1ee7/OpenCloudEnvMonitor/Doc/hardware/Nordic开发板资料/nRF51822AKII/原理图/USBDongle原理图_PCB.PDF

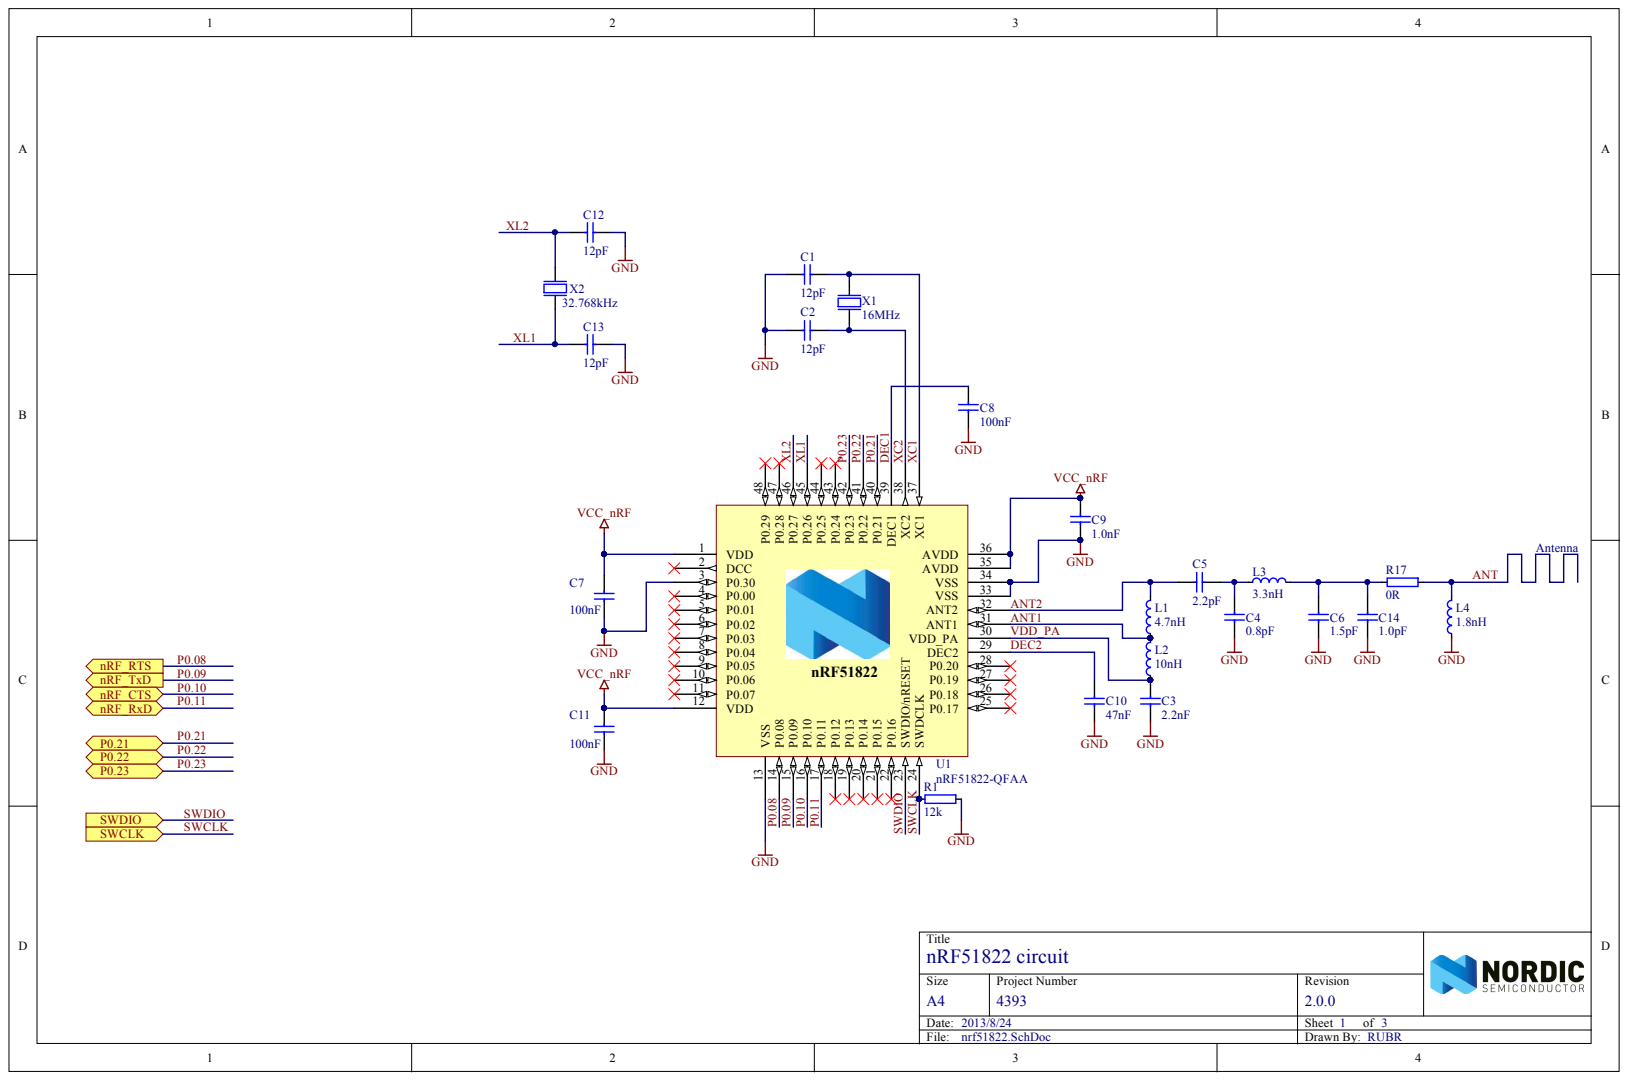
[picture p52: page 1]

VDD_P A
DEC 2

Title Size nRF51822 circuit

A4 | P roje ct Numbe r 4393 | R evision 2.0.0

Date : 2013/8/24 | She et of
File : nr f51822. S chDoc | Dr awn By: RUB R

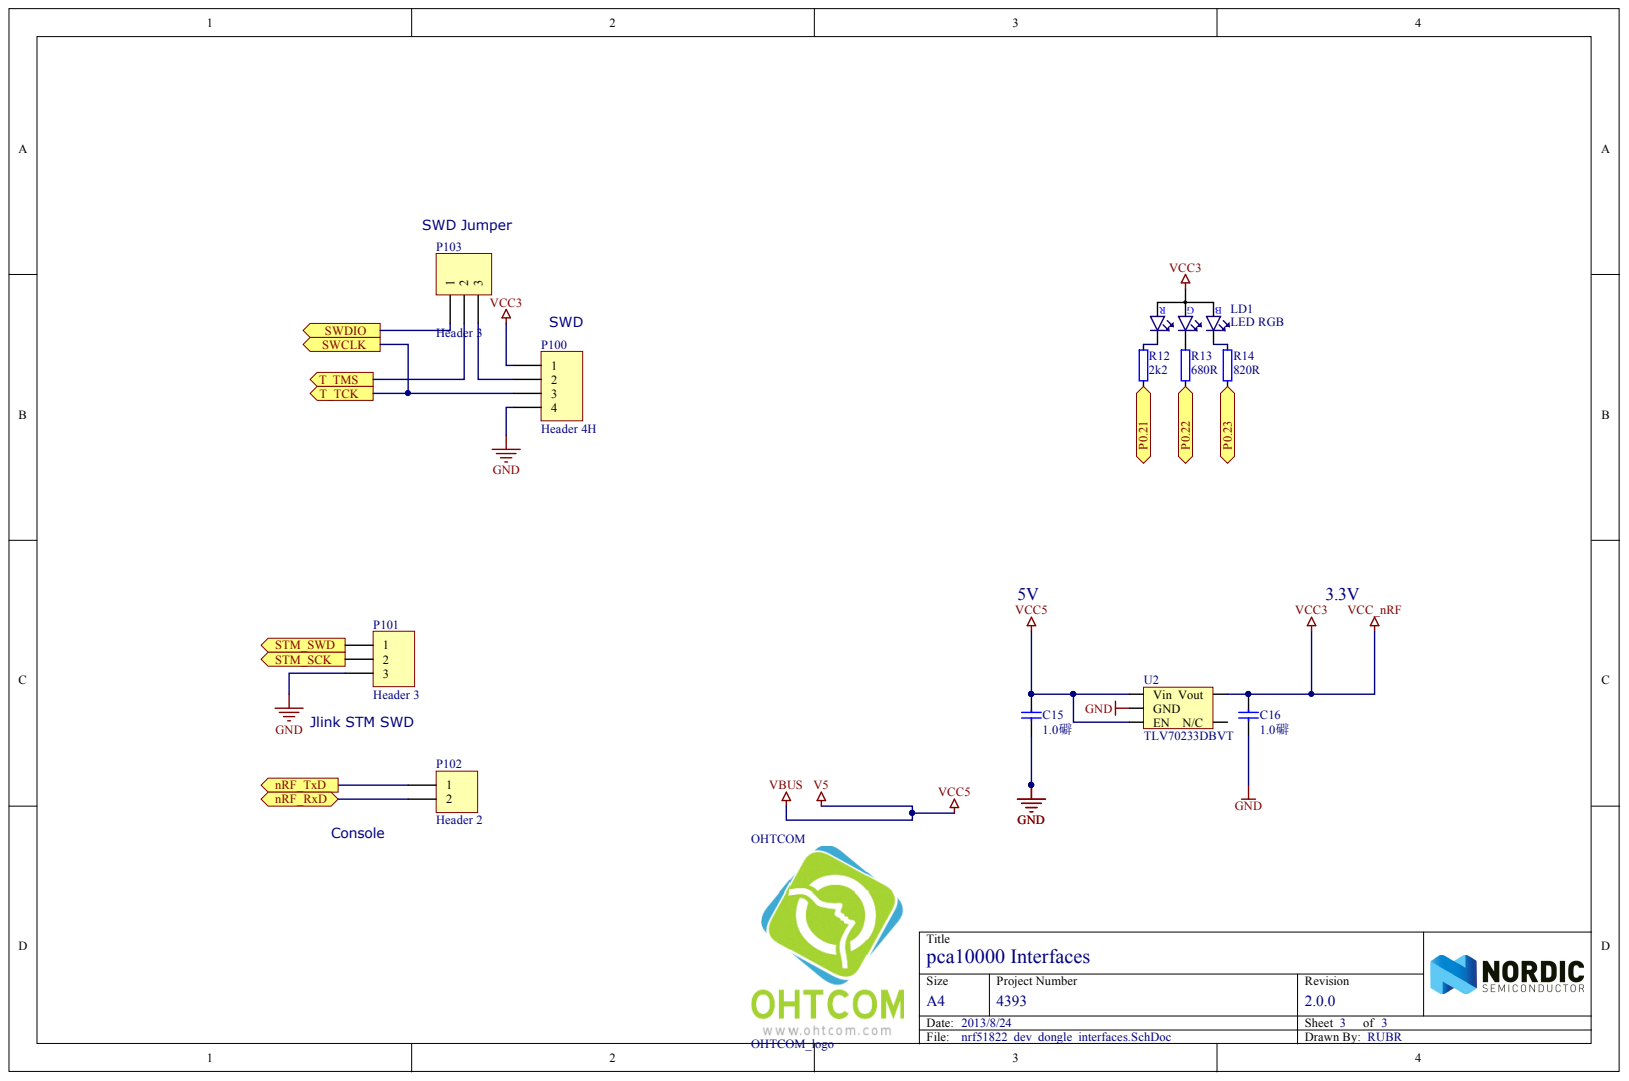
[picture p53: page 2]

Title pca10000 Interfaces

Size A4 | Project Number 4393 | Revision 2.0.0

Date: 2013/8/24 | Sheet 3 of 3
File: nrf51822_dev_dongle_interfaces.SchDoc | Drawn By: RUBR

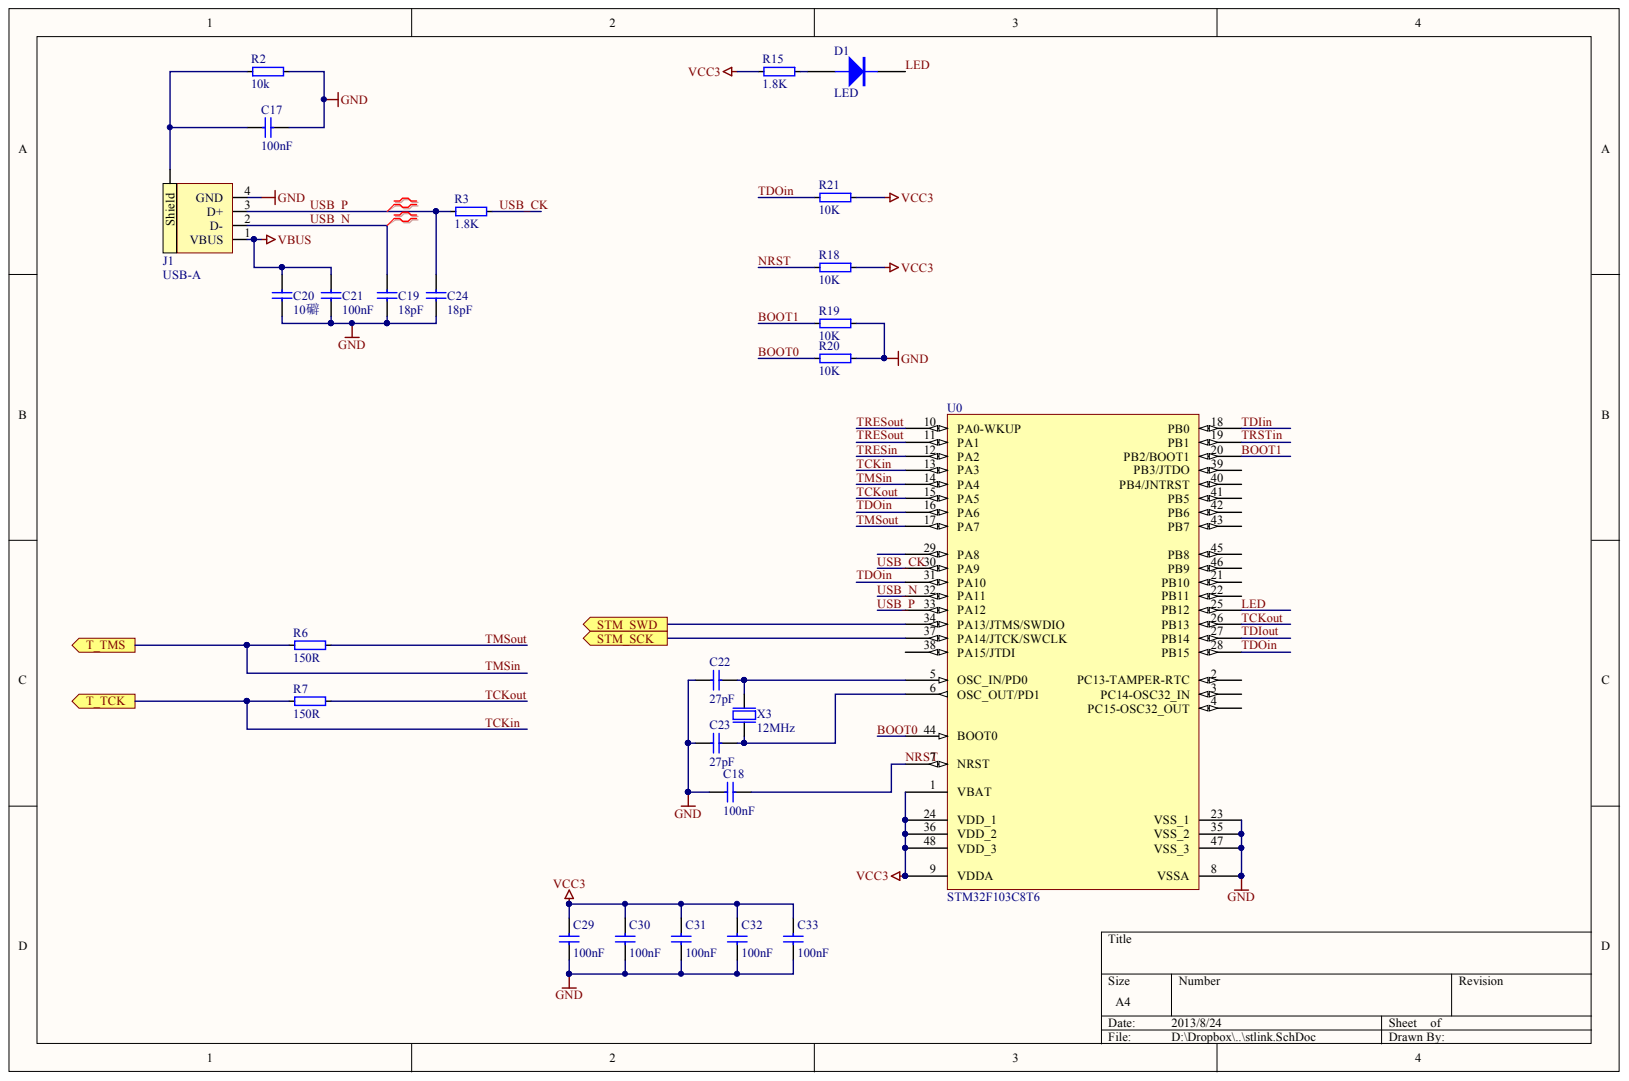
[picture p54: page 3]

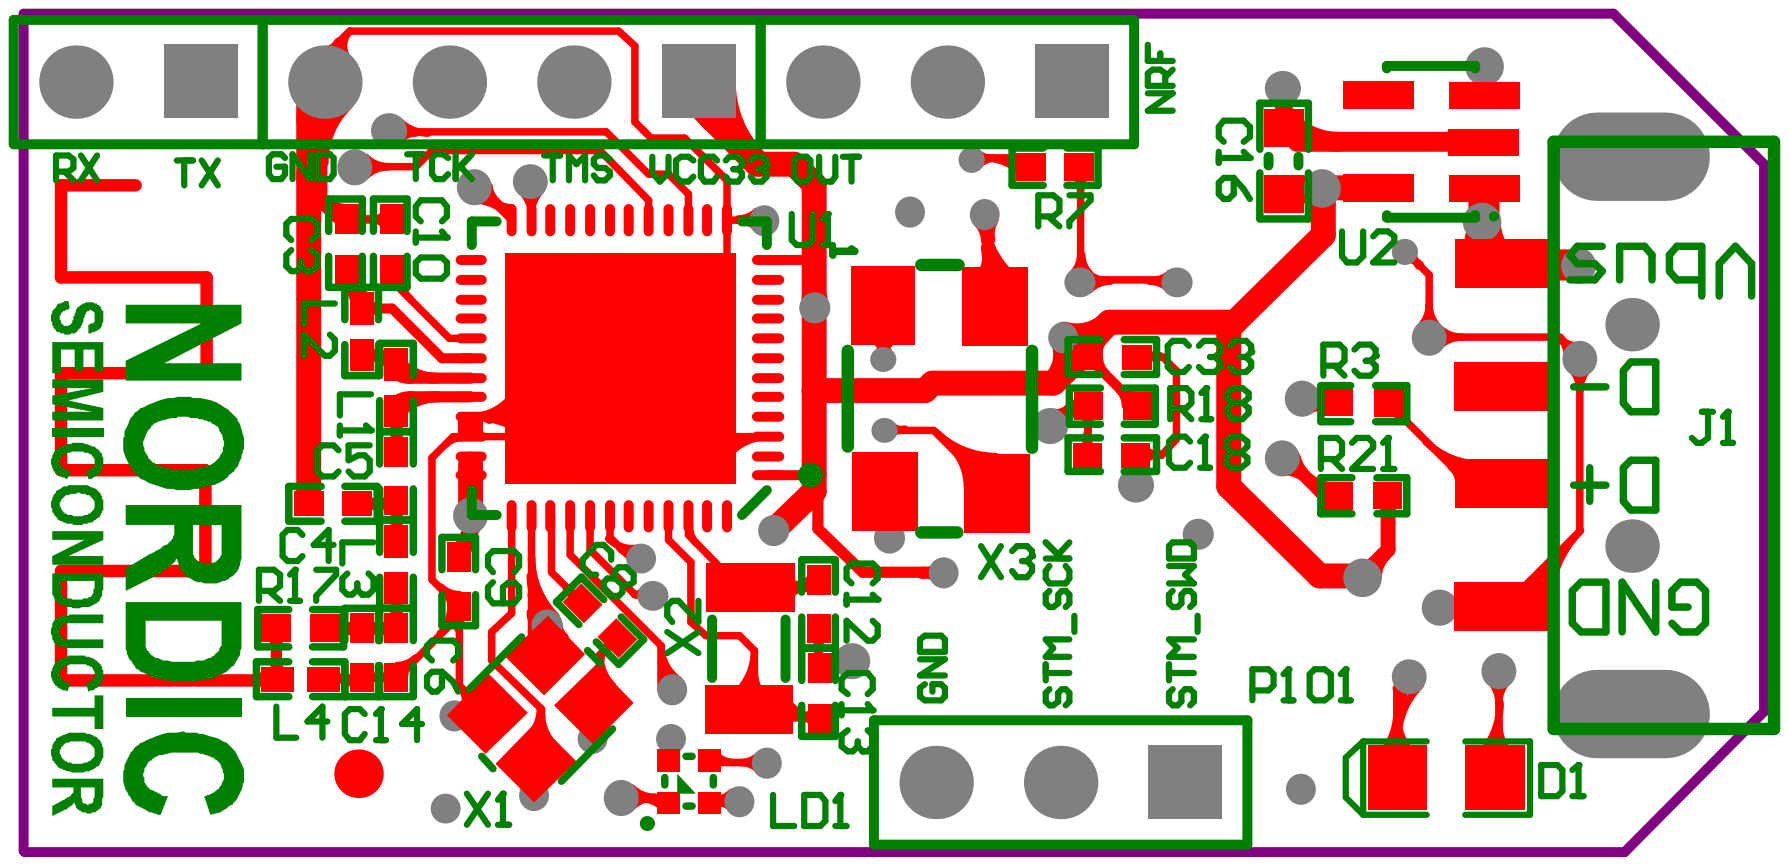
[picture p55: page 4]

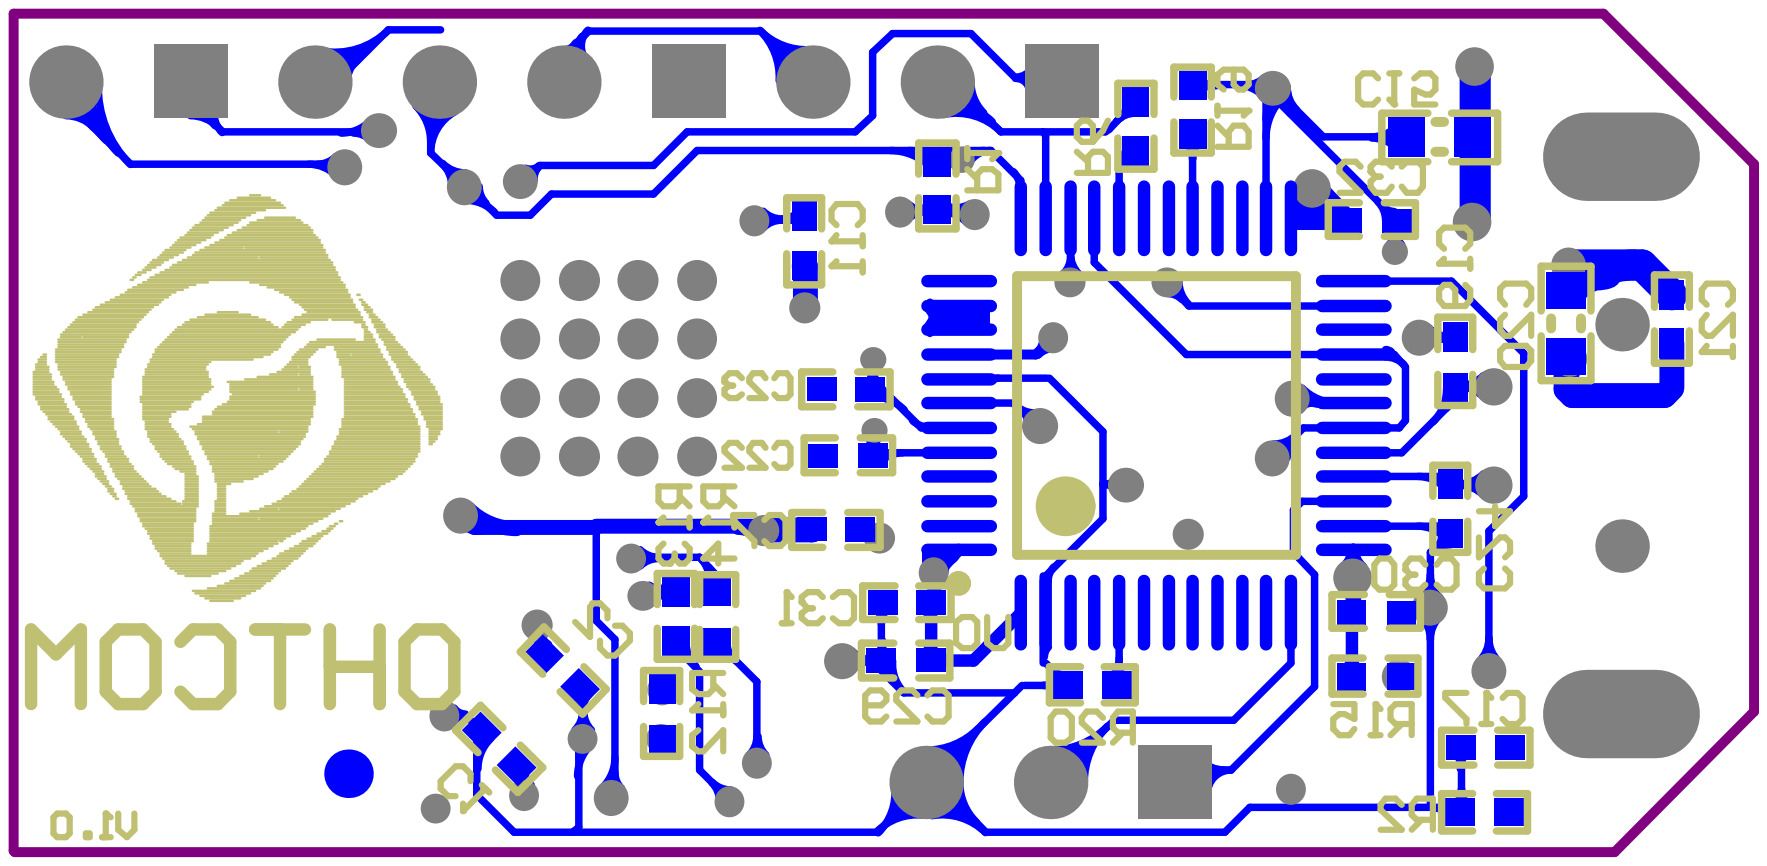
[picture p56: page 5]
