1ee7/OpenCloudEnvMonitor/Src/Include/ext_sensors/.leo_shadow/xadns2080.h

//@+leo-ver=4-thin
//@+node:gan0ling.20140624153650.3688:@shadow adns2080.h
//@@language c
//@@tabwidth -4
//@+others
//@-others
 /* Copyright (c) 2009 Nordic Semiconductor. All Rights Reserved.
 *
 * The information contained herein is property of Nordic Semiconductor ASA.
 * Terms and conditions of usage are described in detail in NORDIC
 * SEMICONDUCTOR STANDARD SOFTWARE LICENSE AGREEMENT.
 *
 * Licensees are granted free, non-transferable use of the information. NO
 * WARRANTY of ANY KIND is provided. This heading must NOT be removed from
 * the file.
 *
 */

#ifndef ADNS2080_H
#define ADNS2080_H

/*lint ++flb "Enter library region" */

#include <stdbool.h>
#include <stdint.h>

/** @file
* @brief ADNS2080 mouse sensor driver
*
* @defgroup nrf_drivers_adns2080 ADNS2080 driver
* @{
* @ingroup nrf_drivers
* @brief ADNS2080 mouse sensor driver.
*/

/**
 * Describes return values for @ref adns2080_init.
 */
typedef enum
{
  ADNS2080_OK, /*!< Operation was succesful */
  ADNS2080_SERIAL_COMM_FAILURE, /*!< Serial communication failed */
  ADNS2080_CHIP_NOT_DETECTED, /*!< Product/Revision ID was not what was expected */
  ADNS2080_INVALID_PARAMETER /*!< Given parameters were not valid */
} adns2080_status_t;

/**
 * ADNS2080 motion output pin polarity values.
 */
typedef enum
{
  ADNS2080_MOTION_OUTPUT_POLARITY_LOW = 0,  /*!< Motion output polarity active low */
  ADNS2080_MOTION_OUTPUT_POLARITY_HIGH = 1  /*!< Motion output polarity active high */
} motion_output_polarity_t;

/**
 * Motion output pin configuration.
 */
typedef enum
{
  ADNS2080_MOTION_OUTPUT_SENSITIVITY_LEVEL = 0,  /*!< Motion output pin will be driven low/high (depending on the polarity setting) as long as there is motion data in DELTA registers */
  ADNS2080_MOTION_OUTPUT_SENSITIVITY_EDGE = 1  /*!< Motion output pin will be driven low/high (depending on the polarity setting) for 380 ns when motion is detected during rest modes */
} motion_output_sensitivity_t;

/**
 * Mouse sensor resolution values.
 */
typedef enum
{
  ADNS2080_RESOLUTION_250DPI = 1, /*!< 250 dpi resolution */
  ADNS2080_RESOLUTION_500DPI = 2, /*!< 500 dpi resolution */
  ADNS2080_RESOLUTION_1000DPI = 0, /*!< 1000 dpi resolution */
  ADNS2080_RESOLUTION_1250DPI = 3, /*!< 1250 dpi resolution */
  ADNS2080_RESOLUTION_1500DPI = 4, /*!< 1500 dpi resolution */
  ADNS2080_RESOLUTION_1750DPI = 5, /*!< 1750 dpi resolution */
  ADNS2080_RESOLUTION_2000DPI = 6 /*!< 2000 dpi resolution */
} adns2080_resolution_t;

/**
 * Mouse sensor forced mode options.
 */
typedef enum
{
  ADNS2080_MODE_NORMAL = 0, /*!< Normal operation mode */
  ADNS2080_MODE_REST1 = 1, /*!< Rest1 operation mode */
  ADNS2080_MODE_REST2 = 2, /*!< Rest2 operation mode */
  ADNS2080_MODE_REST3 = 3, /*!< Rest3 operation mode */
  ADNS2080_MODE_RUN1 = 4, /*!< Run1 operation mode */
  ADNS2080_MODE_RUN2 = 5, /*!< Run2 operation mode */
  ADNS2080_MODE_IDLE = 6 /*!< Idle operation mode */
} adns2080_mode_t;

/**
 * Mouse sensor motion reporting bits.
 */
typedef enum
{
  ADNS2080_MOTION_BITS_8 = 0,  /*!< Motion reporting uses 8 bits */
  ADNS2080_MOTION_BITS_12 = 1  /*!< Motion reporting uses 12 bits */
} adns2080_motion_bits_t;

/**
 * @brief Function for initializing the mouse sensor chip.
 *
 * Valid mouse sensor information will be available 50 milliseconds after this
 * function finishes.
 * 
 * @return 
 * @retval ADNS2080_OK Mouse sensor was initialized succesfully.
 * @retval ADNS2080_SERIAL_COMM_FAILURE Serial communications failure.
 * @retval ADNS2080_CHIP_NOT_DETECTED Could not find revision 0 ADNS2080 chip.
 */
adns2080_status_t adns2080_init(void);

/**
 * @brief Function for resetting the mouse sensor chip.
 *
 * Valid mouse sensor information will be available 50 milliseconds after this
 * function finishes.
 * All register settings will be lost and need to be reloaded.
 * 
 */
void adns2080_reset(void);
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
